antomicblitz/hf-game-controller-workshop/tests/test_case_execution.py

"""Behavioral tests for the fail-closed CAD execution boundary."""

from __future__ import annotations

import ctypes
import errno
import json
import os
import resource
import runpy
import shutil
import socket
import subprocess
import sys
import threading
from collections.abc import Generator
from contextlib import contextmanager
from pathlib import Path
from typing import Any, cast
from unittest import mock

import pytest

_here = Path(__file__).resolve().parent
_session = _here.parent
sys.path.insert(0, str(_session / "tools"))


@contextmanager
def _noop_seccomp_filter() -> Generator[None, None, None]:
    yield


def test_linux_probe_requires_network_namespace(monkeypatch: pytest.MonkeyPatch) -> None:
    from cadkit import _sandbox

    seen: list[list[str]] = []

    def runner(command: list[str], **_kwargs: object) -> subprocess.CompletedProcess[str]:
        seen.append(command)
        return subprocess.CompletedProcess(command, 0, "", "")

    def fake_which(_name: str) -> str:
        return "/fake/bwrap"

    monkeypatch.setattr(_sandbox.shutil, "which", fake_which)
    available, reason = _sandbox._probe_linux(runner)  # pyright: ignore[reportPrivateUsage]

    assert available is True
    assert reason == "bubblewrap network namespace available"
    assert "--unshare-net" in seen[0]


def test_linux_status_prefers_direct_probe(monkeypatch: pytest.MonkeyPatch) -> None:
    from cadkit import _sandbox

    probes: list[str] = []

    def direct_probe() -> tuple[bool, str]:
        probes.append("direct")
        return True, "direct probe passed"

    def fallback_probe() -> tuple[bool, str]:
        probes.append("fallback")
        raise AssertionError("fallback must not run after a successful direct probe")

    monkeypatch.setattr(_sandbox.platform, "system", lambda: "Linux")
    monkeypatch.setattr(_sandbox, "_probe_linux", direct_probe)
    monkeypatch.setattr(_sandbox, "_probe_linux_unshare", fallback_probe)
    monkeypatch.setattr(_sandbox, "seccomp_filter", _noop_seccomp_filter)

    assert _sandbox.status() == (True, "bubblewrap", "direct probe passed")
    assert probes == ["direct"]


def test_linux_status_selects_unshare_after_direct_failure(
    monkeypatch: pytest.MonkeyPatch,
) -> None:
    from cadkit import _sandbox

    probes: list[str] = []

    def direct_probe() -> tuple[bool, str]:
        probes.append("direct")
        return False, "direct probe failed"

    def fallback_probe() -> tuple[bool, str]:
        probes.append("fallback")
        return True, "wrapped probe passed"

    monkeypatch.setattr(_sandbox.platform, "system", lambda: "Linux")
    monkeypatch.setattr(_sandbox, "_probe_linux", direct_probe)
    monkeypatch.setattr(_sandbox, "_probe_linux_unshare", fallback_probe)
    monkeypatch.setattr(_sandbox, "seccomp_filter", _noop_seccomp_filter)

    assert _sandbox.status() == (True, "bubblewrap-unshare", "wrapped probe passed")
    assert probes == ["direct", "fallback"]
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
